ak66666/ThumbsUpV7Rp2040MX/Photos/IMG_20231021_212923854.jpg

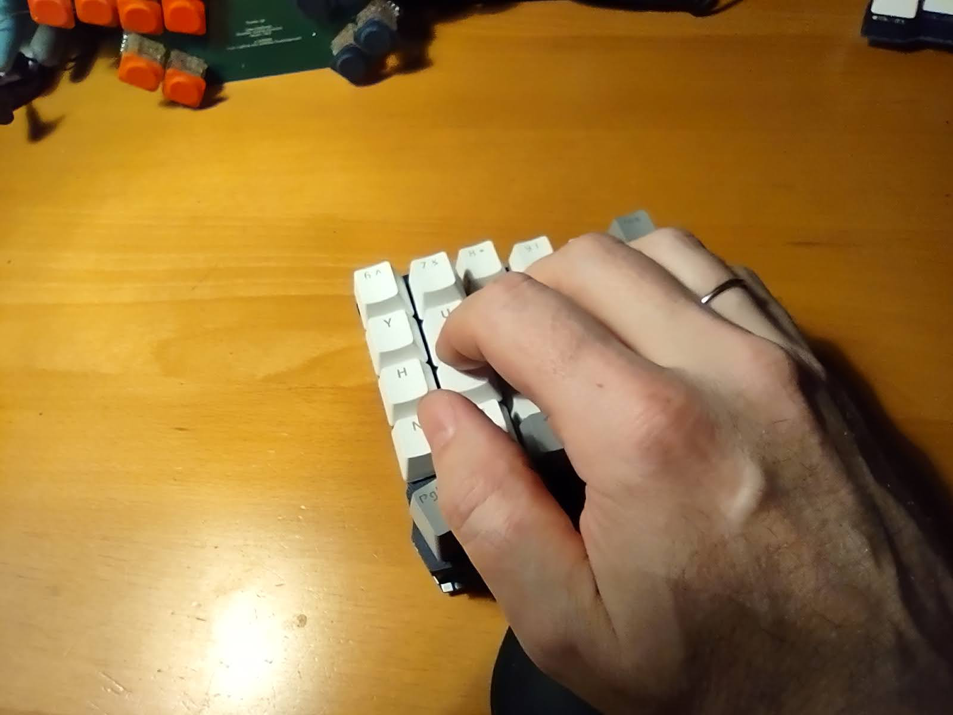
Photos/IMG_20231021_212923854.jpg
