ak66666/ThumbsUpV7Rp2040MX/Photos/IMG_20231021_213024446.jpg

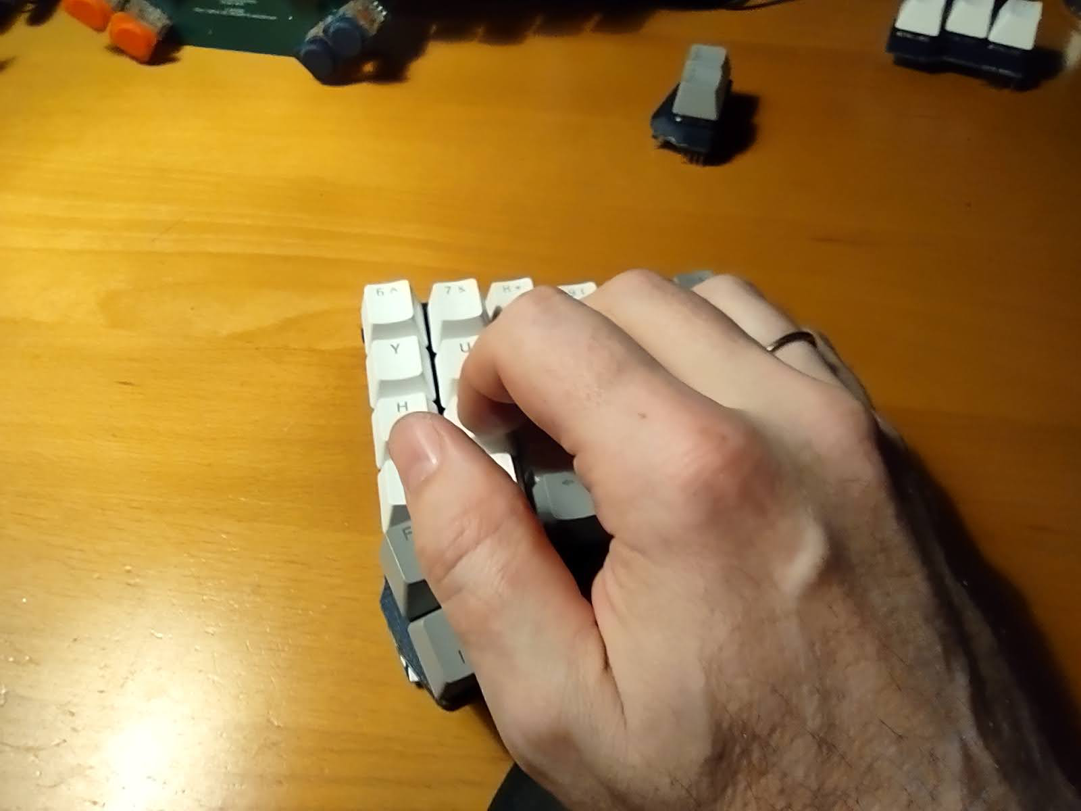
Photos/IMG_20231021_213024446.jpg
