ak66666/ThumbsUpV7Rp2040MX/Photos/IMG_20231021_213114463_HDR.jpg

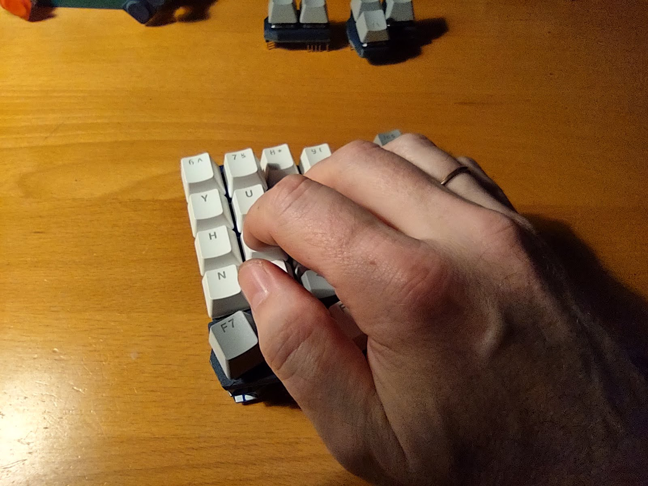
Photos/IMG_20231021_213114463_HDR.jpg
