ak66666/ThumbsUpV7Rp2040MX/Photos/IMG_20231021_213127833.jpg

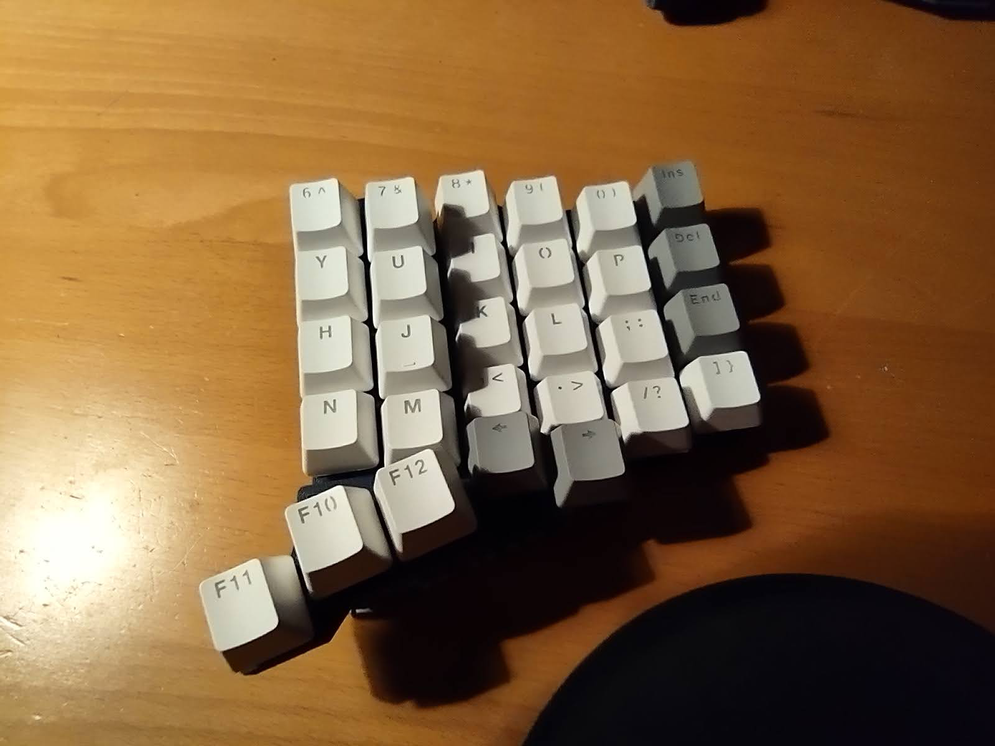
Photos/IMG_20231021_213127833.jpg
