ak66666/ThumbsUpV7Rp2040MX/Photos/IMG_20231021_213133426_HDR.jpg

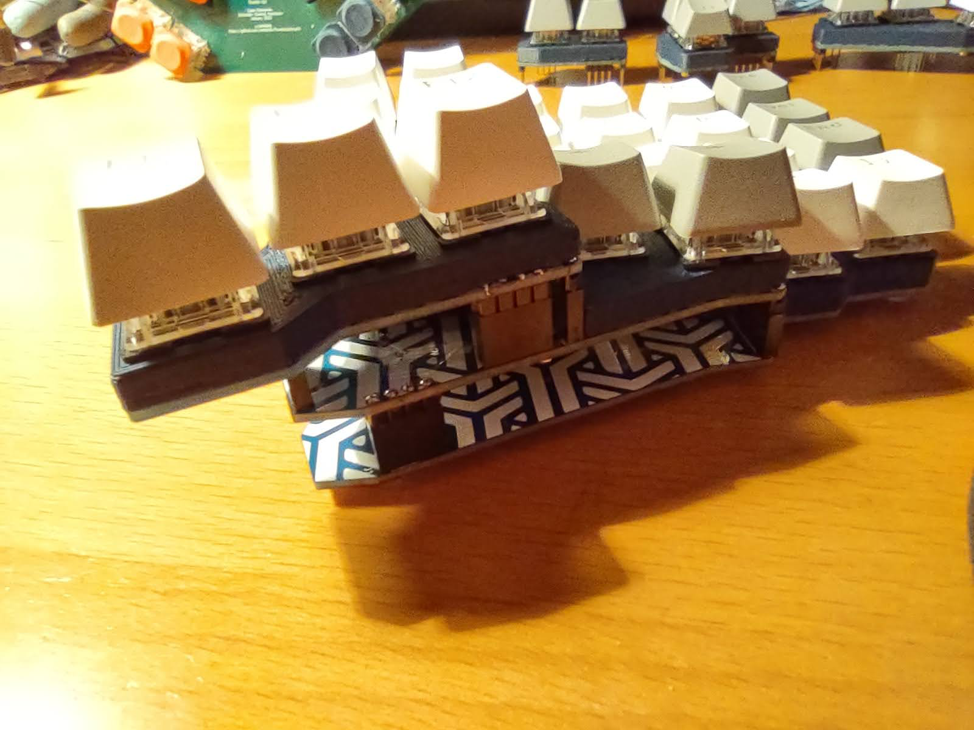
Photos/IMG_20231021_213133426_HDR.jpg
