ak66666/ThumbsUpV7Rp2040MX/Photos/IMG_20231024_213244499.jpg

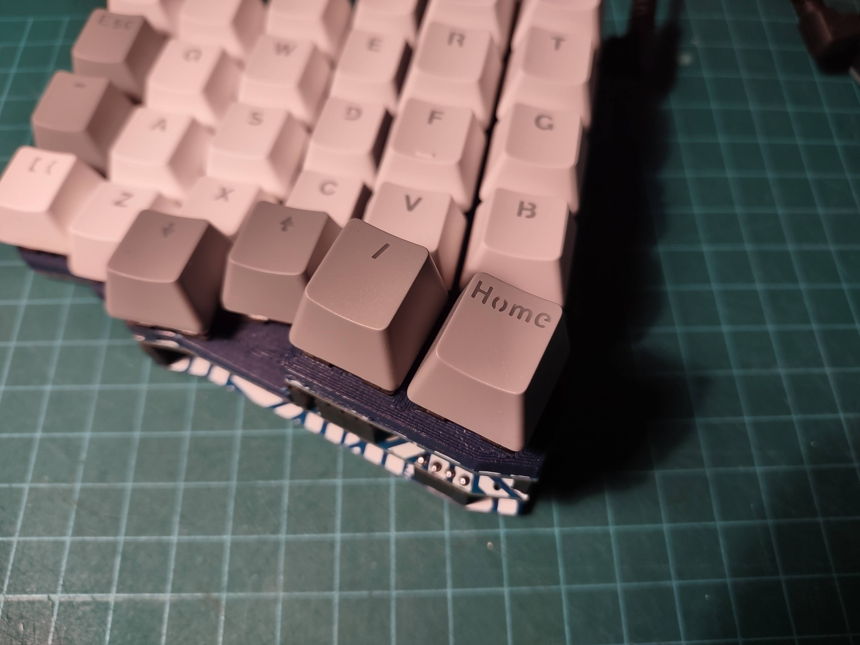
Photos/IMG_20231024_213244499.jpg
