ak66666/ThumbsUpV7Rp2040MX/Photos/IMG_20231024_213355412_HDR.jpg

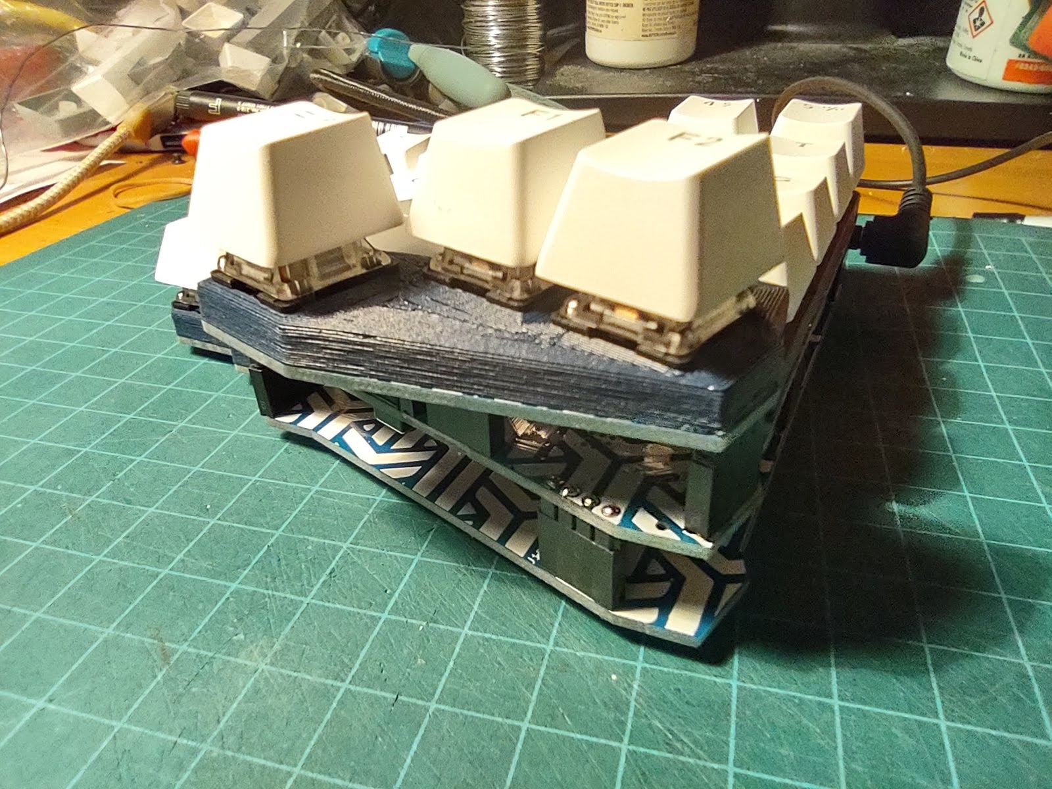
Photos/IMG_20231024_213355412_HDR.jpg
