ak66666/ThumbsUpV7Rp2040MX/Photos/IMG_20231025_101417310_HDR.jpg

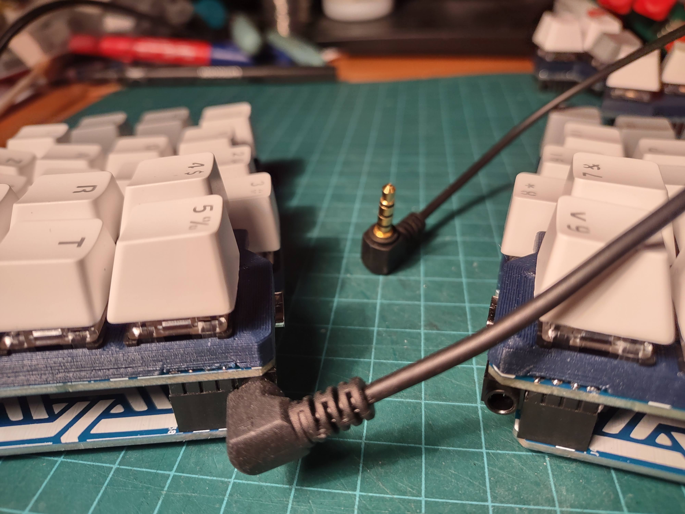
Photos/IMG_20231025_101417310_HDR.jpg
